mocketech/EmoGo/stone/codes/stone/data/240x240/dead_black.png

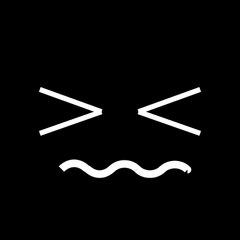
stone/codes/stone/data/240x240/dead_black.png
