mocketech/EmoGo/stone/codes/stone/data/240x240/dead_blink.png

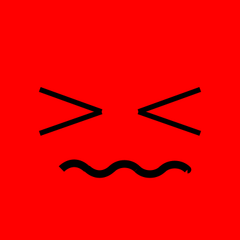
stone/codes/stone/data/240x240/dead_blink.png
