mocketech/EmoGo/stone/codes/stone/data/240x240/defensive_black.png

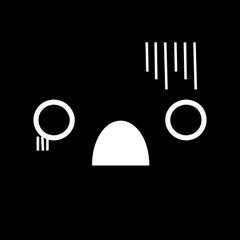
stone/codes/stone/data/240x240/defensive_black.png
