mocketech/EmoGo/stone/codes/stone/data/240x240/defensive_blink.png

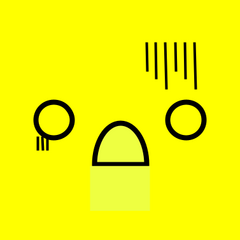
stone/codes/stone/data/240x240/defensive_blink.png
