mocketech/EmoGo/stone/codes/stone/data/240x240/normal_black.png

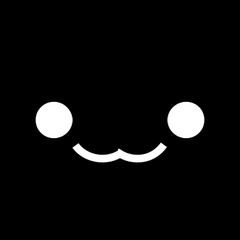
stone/codes/stone/data/240x240/normal_black.png
