mocketech/EmoGo/stone/codes/stone/data/240x240/normal_blink.png

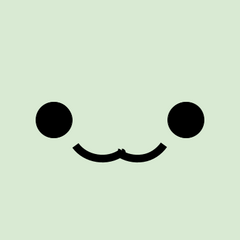
stone/codes/stone/data/240x240/normal_blink.png
