mocketech/EmoGo/stone/codes/stone/data/240x240/offensive_black.png

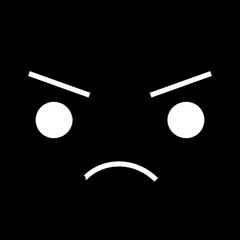
stone/codes/stone/data/240x240/offensive_black.png
