mocketech/EmoGo/stone/codes/stone/data/240x240/offensive_blink.png

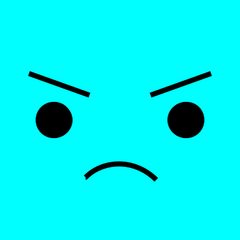
stone/codes/stone/data/240x240/offensive_blink.png
